TechxArtisanStudio/Openterface_KVM-GO_Hardware/models/DP/KVM_Go_DP.png

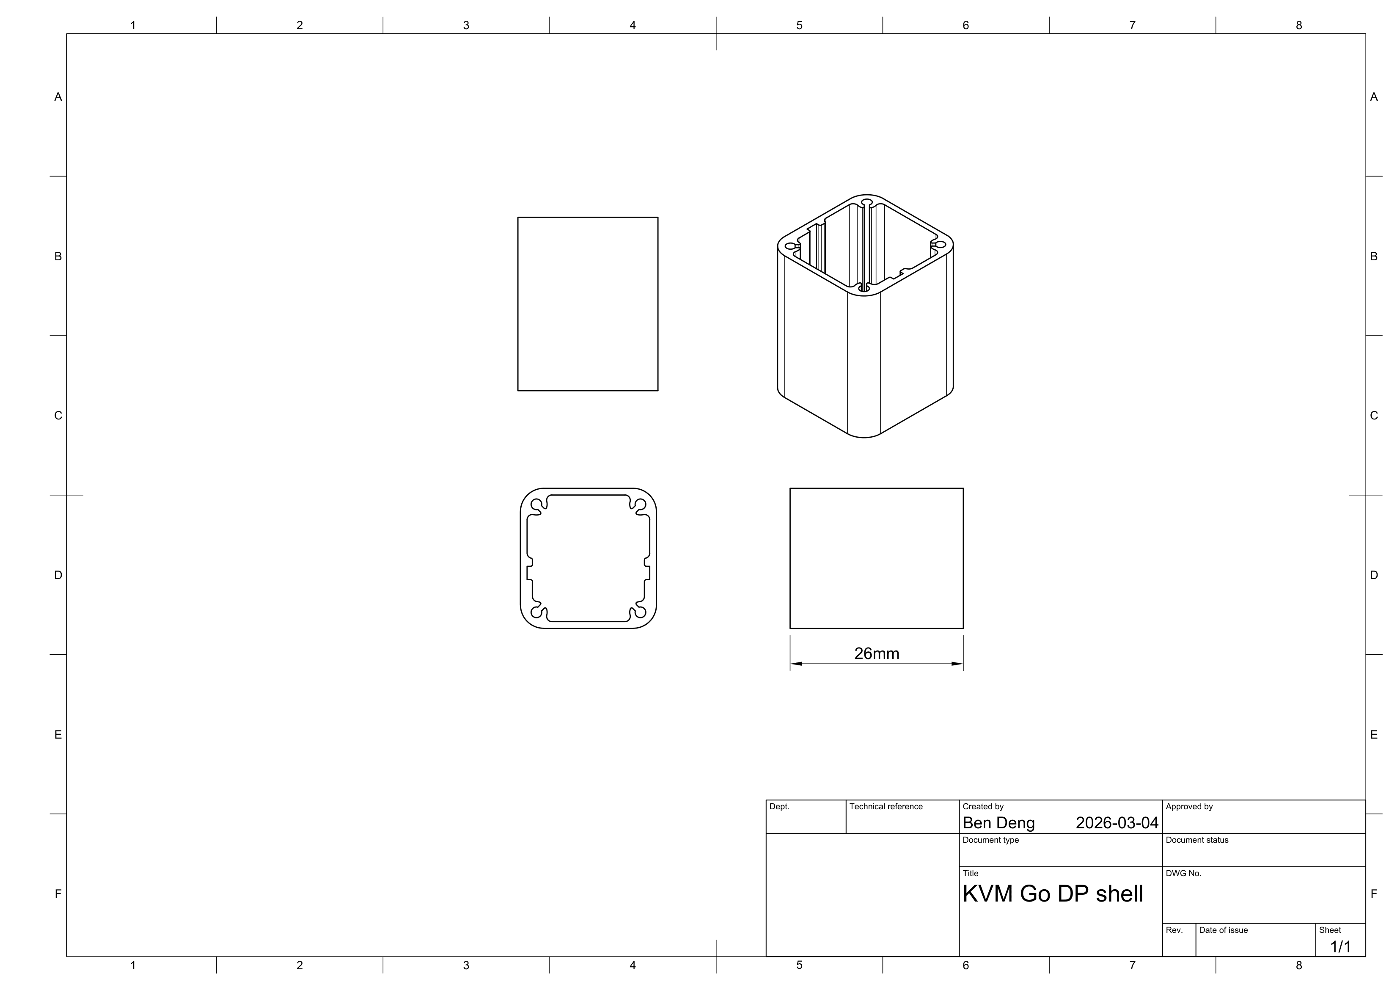
models/DP/KVM_Go_DP.png
